K1P5/Nanofeed-2.0/Images/Nanofeed Cutaway A.JPG

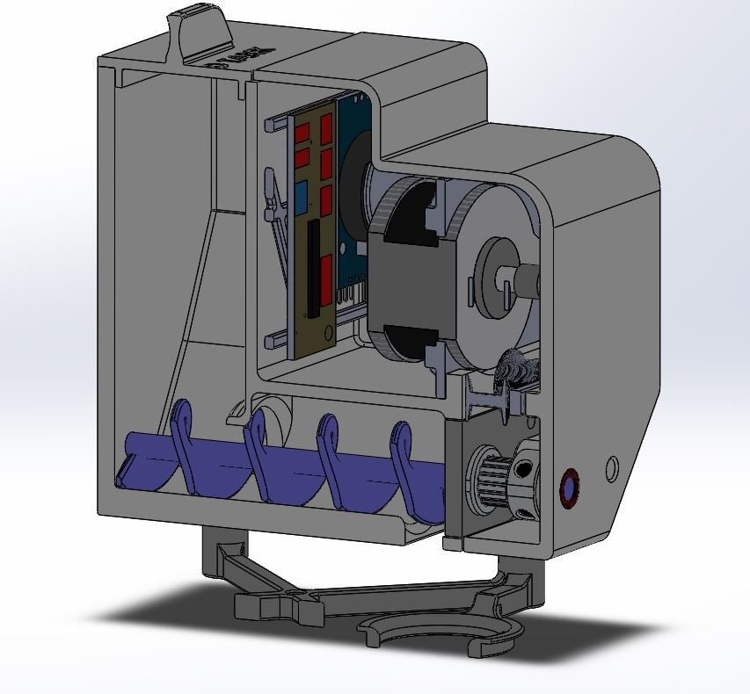
Images/Nanofeed Cutaway A.JPG
