K1P5/Nanofeed-2.0/Images/Nanofeed Iso View B.JPG

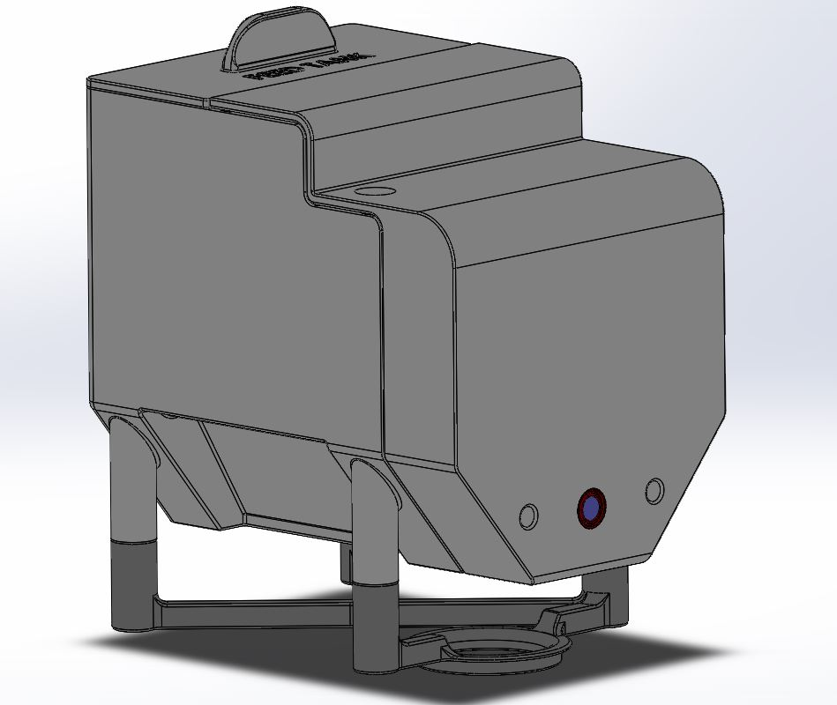
Images/Nanofeed Iso View B.JPG
