K1P5/Nanofeed-2.0/Images/REF IMAGE 2.jpeg

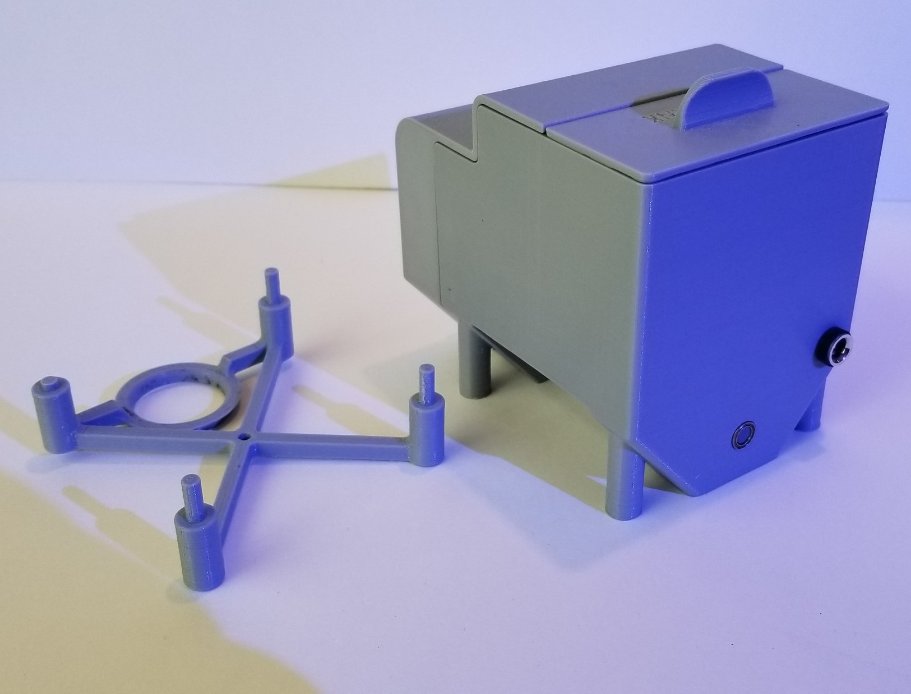
Images/REF IMAGE 2.jpeg
