K1P5/Nanofeed-2.0/Images/REF IMAGE 3.jpeg

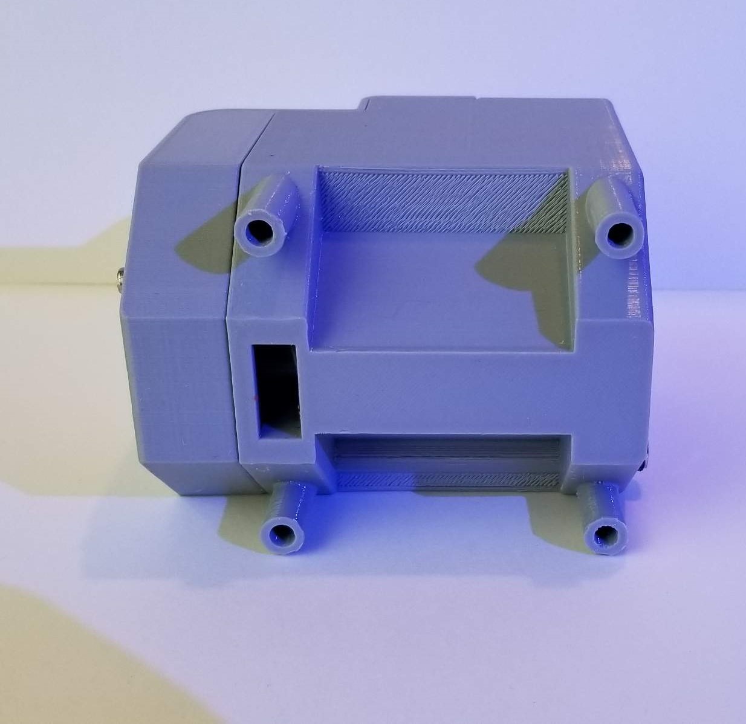
Images/REF IMAGE 3.jpeg
