K1P5/Nanofeed-2.0/Images/REF IMAGE 4.jpeg

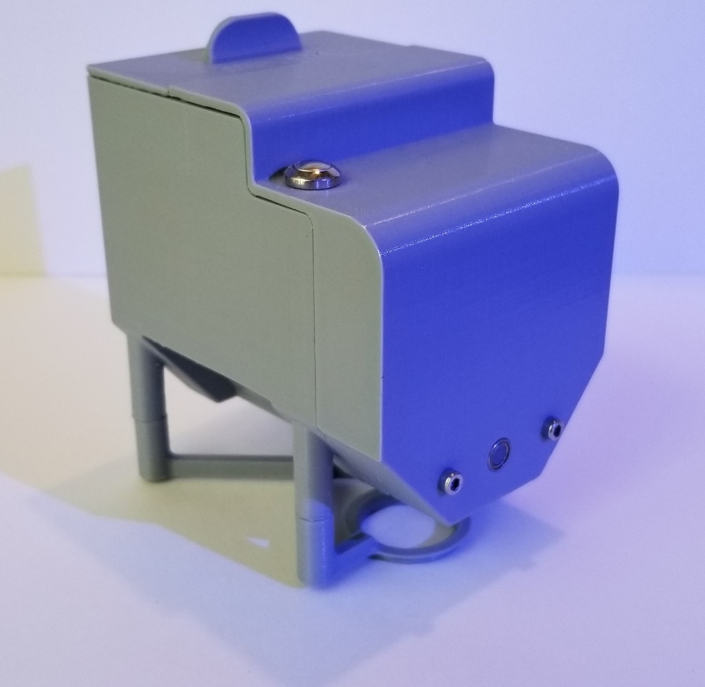
Images/REF IMAGE 4.jpeg
