K1P5/Nanofeed-2.0/Images/Resized_20210130_144933.jpeg

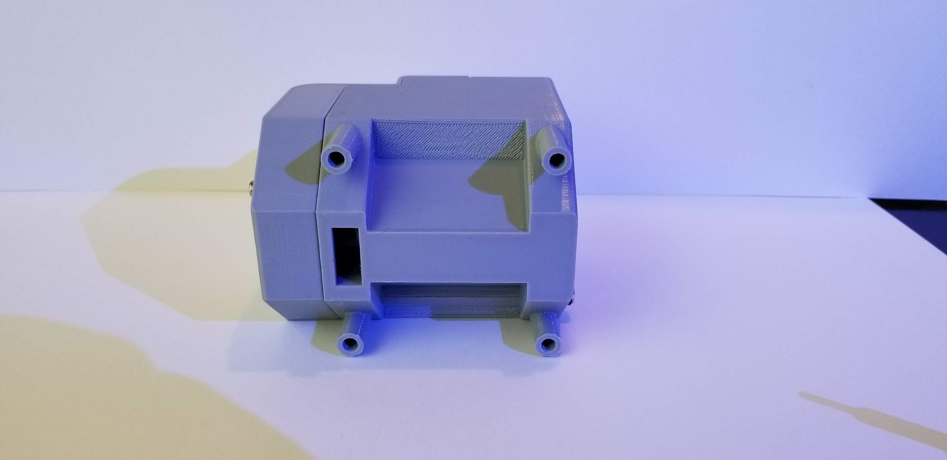
Images/Resized_20210130_144933.jpeg
